G14D0s/VFD-Clock/Documentation/Ablauf_Multiplexing_VFD.png

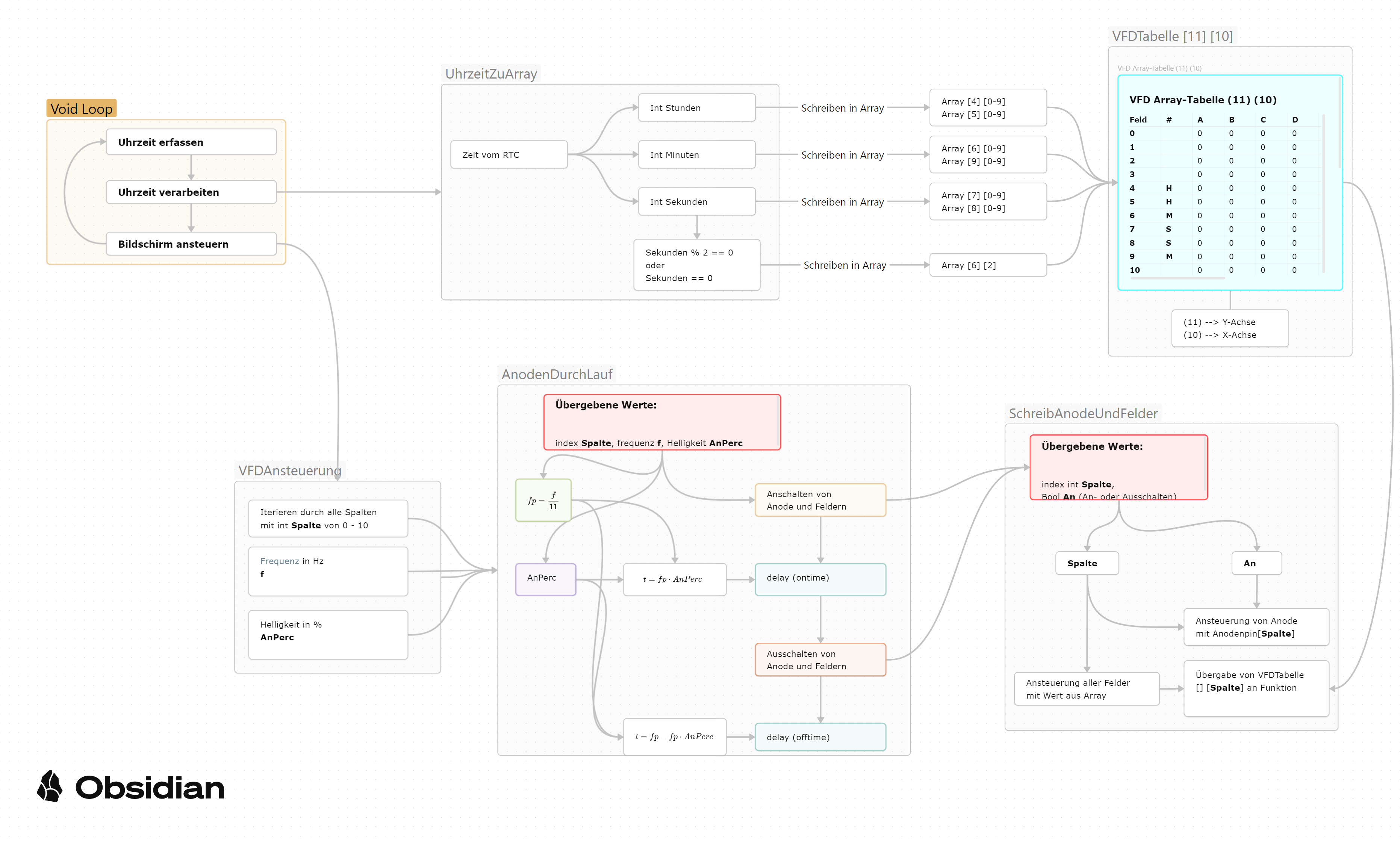
Documentation/Ablauf_Multiplexing_VFD.png
